clickworkorange/tp770cf/TP770_IDE.sch

## KiCad design TP770_IDE.sch (2022-01-22)

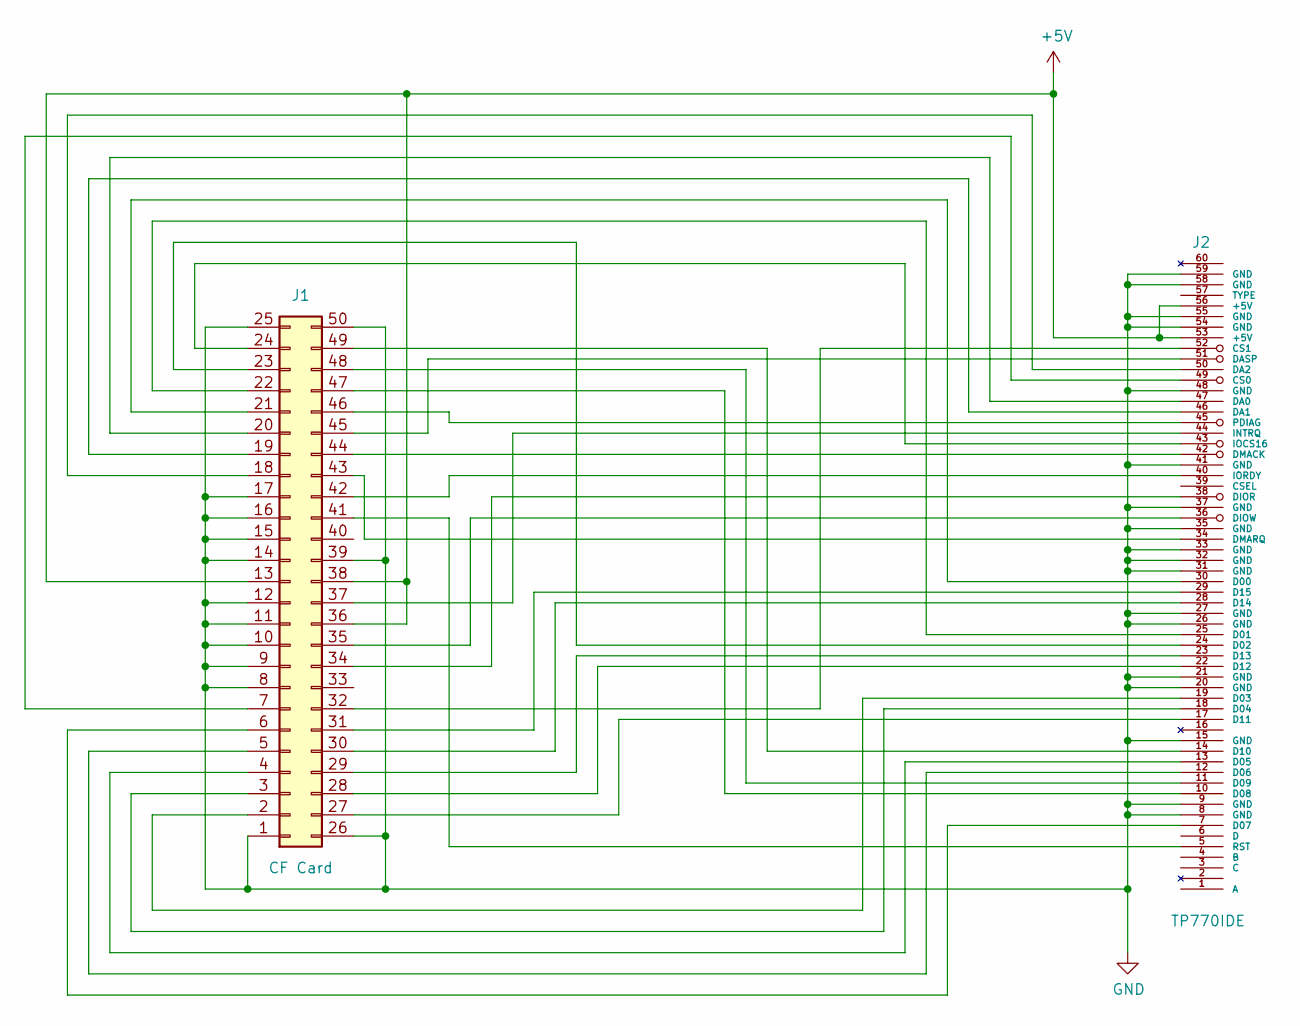
[picture p3: schematic TP770_IDE.sch]

Parts:
J1: CF Card; CF-Card_3M_N7E50-7516PK-20-WF
J2: TP770IDE

Connections:
+5V: J1.13, J1.36, J1.38, J2.53 (+5V), J2.56 (+5V)
GND: J1.1, J1.8, J1.9, J1.10, J1.11, J1.12, J1.14, J1.15, J1.16, J1.17, J1.25, J1.26, J1.39, J1.50, J2.8 (GND), J2.9 (GND), J2.15 (GND), J2.20 (GND), J2.21 (GND), J2.26 (GND), J2.27 (GND), J2.31 (GND), J2.32 (GND), J2.33 (GND), J2.35 (GND), J2.37 (GND), J2.41 (GND), J2.48 (GND), J2.54 (GND), J2.55 (GND), J2.58 (GND), J2.59 (GND)
unnamed: J1.2, J2.19 (D03)
unnamed: J1.3, J2.18 (D04)
unnamed: J1.4, J2.13 (D05)
unnamed: J1.5, J2.12 (D06)
unnamed: J1.6, J2.7 (D07)
unnamed: J1.7, J2.49 (CS0)
unnamed: J1.18, J2.50 (DA2)
unnamed: J1.19, J2.46 (DA1)
unnamed: J1.20, J2.47 (DA0)
unnamed: J1.21, J2.30 (D00)
unnamed: J1.22, J2.25 (D01)
unnamed: J1.23, J2.24 (D02)
unnamed: J1.24, J2.43 (IOCS16)
unnamed: J1.27, J2.17 (D11)
unnamed: J1.28, J2.22 (D12)
unnamed: J1.29, J2.23 (D13)
unnamed: J1.30, J2.28 (D14)
unnamed: J1.31, J2.29 (D15)
unnamed: J1.32, J2.52 (CS1)
unnamed: J1.34, J2.38 (DIOR)
unnamed: J1.35, J2.36 (DIOW)
unnamed: J1.37, J2.44 (INTRQ)
unnamed: J1.41, J2.5 (RST)
unnamed: J1.42, J2.40 (IORDY)
unnamed: J1.43, J2.34 (DMARQ)
unnamed: J1.44, J2.42 (DMACK)
unnamed: J1.45, J2.51 (DASP)
unnamed: J1.46, J2.45 (PDIAG)
unnamed: J1.47, J2.10 (D08)
unnamed: J1.48, J2.11 (D09)
unnamed: J1.49, J2.14 (D10)
